seidenstrasse/sss7modem/hardware/artwork/seidenstrasse.png

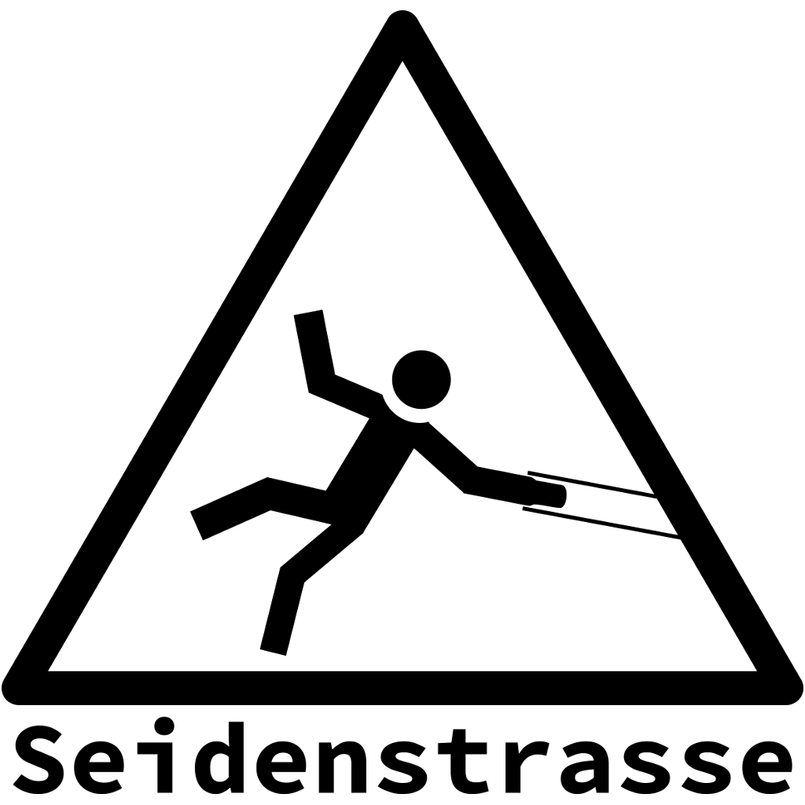
hardware/artwork/seidenstrasse.png
